ZDohaim/ECE445-MTD-Tracker/notebooks/Amber/pcb/mtd_pcb.kicad_pcb

## KiCad design flipper42_cad/flipper42.kicad_sch


Parts:
IC1: EM4095; SO16
J1: 1040310811; 104031-0811_MOL
U1: ST25R3916B-AQWT; VFQFPN32_5X5_WETTABLE_STM
